Mark-MDO47/RingTheBell/code/lib_commonDFcode/lib_commonDFcode.h

// This ".h" file is actually C-code. Saves me the need to turn it into a true library.

/////////////////////////////////////////////////////////////////////////////////////////////////////////
#if DFPRINTDETAIL
void DFprintDetail(uint8_t type, int value){
  switch (type) {
    case TimeOut:
      Serial.println(F("Time Out!")); break;
    case WrongStack:
      Serial.println(F("Stack Wrong!")); break;
    case DFPlayerCardInserted:
      Serial.println(F("Card Inserted!")); break;
    case DFPlayerCardRemoved:
      Serial.println(F("Card Removed!")); break;
    case DFPlayerCardOnline:
      Serial.println(F("Card Online!")); break;
    case DFPlayerUSBInserted:
      Serial.println("USB Inserted!"); break;
    case DFPlayerUSBRemoved:
      Serial.println("USB Removed!"); break;
    case DFPlayerPlayFinished:
      Serial.print(F("Number:")); Serial.print(value); Serial.println(F(" Play Finished!"));  break;
    case DFPlayerError:
      Serial.print(F("DFPlayerError:"));
      switch (value) {
        case Busy:
          Serial.println(F("Card not found"));
          break;
        case Sleeping:
          Serial.println(F("Sleeping"));
          break;
        case SerialWrongStack:
          Serial.println(F("Get Wrong Stack"));
          break;
        case CheckSumNotMatch:
          Serial.println(F("Check Sum Not Match"));
          break;
        case FileIndexOut:
          Serial.println(F("File Index Out of Bound"));
          break;
        case FileMismatch:
          Serial.println(F("Cannot Find File"));
          break;
        case Advertise:
          Serial.println(F("In Advertise"));
          break;
        default:
          break;
      } // end switch (value)
      break;
    default:
      break;
  }  // end switch (type)
} // end DFprintDetail()
#endif // DFPRINTDETAIL

/////////////////////////////////////////////////////////////////////////////////////////////////////////
// DFstartSound(p_SoundNum, p_Volume) - start p_SoundNum if it is valid
//
// p_SoundNum is the sound file number, range 1 to SOUNDNUM_MAX_VALID
// p_Volume   is the requested vol, range 0 to 30
//
// Had lots of trouble with reliable operation using playMp3Folder. Came to conclusion
//    that it is best to use the most primitive of YX5200 commands.
// Also saw strong correlation of using YX5200 ACK and having even more unreliable
//    operation, so turned that off in DFinit.
// The code checking DPIN_AUDIO_BUSY still needs the delay but 200 millisec is probably overkill.
// There is code checking myDFPlayer.available() that can maybe also be removed now
//    that the dubugging for above is finished. Now that I am using myDFPlayer.play(),
//    it only seems to trigger when I interrupt a playing sound by starting another.
//    It is sort of interesting but not needed.
//
void  DFstartSound(uint16_t p_SoundNum, uint16_t p_Volume) {
  uint16_t idx;
  bool prevHI;
  uint16_t my_SoundNum = p_SoundNum;
  static uint8_t init_minmax = 2;
  static uint32_t prev_msec;
  static uint32_t max_msec = 0;
  static uint32_t min_msec = 999999;
  uint32_t diff_msec = 0;
  uint32_t now_msec = millis();

#if DFPRINTDETAIL
  if (myDFPlayer.available()) {
    Serial.print(F(" DFstartSound ln ")); Serial.print((uint16_t) __LINE__); Serial.println(F(" myDFPlayer problem after volume"));
    DFprintDetail(myDFPlayer.readType(), myDFPlayer.read()); //Print the detail message from DFPlayer to handle different errors and states.
  }
#endif // DFPRINTDETAIL

  myDFPlayer.volume(p_Volume);  // Set volume value. Range from 0 to 30
  myDFPlayer.play(my_SoundNum); //play specific wav in SD: root directory ###.wav; number played is physical copy order; first one copied is 1
  // Serial.print(F("DEBUG DFstartSound myDFPlayer.play(")); Serial.print((uint16_t) my_SoundNum); Serial.println(F(")"));
  gTimerForceSoundActv = millis() + SOUND_ACTIVE_PROTECT; // handle YX5200 problem with interrupting play

  if (init_minmax) {
    init_minmax -= 1;
  }  else {
    diff_msec = now_msec - prev_msec;
    if (diff_msec > max_msec) {
      max_msec = diff_msec;
      // Serial.print(F("max_msec ")); Serial.println(max_msec);
    } else if (diff_msec < min_msec) {
      min_msec = diff_msec;
      // Serial.print(F("min_msec ")); Serial.println(min_msec);
    }
  }
  prev_msec = now_msec;
} // end DFstartSound()

/////////////////////////////////////////////////////////////////////////////////////////////////////////
// DFcheckSoundDone() - returns TRUE if previous sound is complete (DFPlayer/YX5200 is notBusy)
//
// notBusy means (HIGH == digitalRead(DPIN_AUDIO_BUSY)) && (millis() >= gTimerForceSoundActv)
//
//    DPIN_AUDIO_BUSY goes HIGH when sound finished, but may take a while to start being high after sound starts
//    gTimerForceSoundActv is millisec count we have to wait for to before checking DPIN_AUDIO_BUSY
//    so we have to be BOTH (DPIN_AUDIO_BUSY is HIGH) AND (current time is beyond gTimerForceSoundActv)
//
uint8_t DFcheckSoundDone() {
  return (HIGH == digitalRead(DPIN_AUDIO_BUSY)) && (millis() >= gTimerForceSoundActv);
} // end DFcheckSoundDone()

/////////////////////////////////////////////////////////////////////////////////////////////////////////
// DFsetup()
void DFsetup() {
  Serial.println(F("Initializing DFPlayer ... (May take 3~5 seconds)"));
  
  pinMode(DPIN_AUDIO_BUSY,  INPUT_PULLUP); // HIGH when audio stops
  Serial2.begin(9600, SERIAL_8N1, DPIN_HWSRL_RX, DPIN_HWSRL_TX); // this is control to DFPlayer audio player 
  if (!myDFPlayer.begin(Serial2, false, true)) {  // Serial2 to communicate with mp3 player
    Serial.println(F("Unable to begin DFPlayer:"));
    Serial.println(F("1.Please recheck the connection!"));
    Serial.println(F("2.Please insert the SD card!"));
    while(true){
      delay(1);
    }
  }
  myDFPlayer.EQ(DFPLAYER_EQ_BASS); // our speaker is quite small
  myDFPlayer.outputDevice(DFPLAYER_DEVICE_SD); // location of sound files is MicroSD card
  myDFPlayer.volume(SOUND_VOL_MAX);  // Set volume value. From 0 to 30 - FIXME 25 is good
  // delay(3000); // allow bluetooth connection to complete - not using bluetooth; tinny sound from small speaker adds to effect
  delay(1000); // allow DFPlayer to stabilize
  Serial.println(F("DFPlayer Mini online."));

} // end DFsetup()
