Mark-MDO47/RingTheBell/code/RingTheBell/SoundNum.h

// DuelWithBanjos
// Author: https://github.com/Mark-MDO47/
//

#ifndef SOUNDNUM_h

#define SOUNDNUM_h

#define SOUNDNUM_MalletHit    1
#define SOUNDNUM_silence      2
#define SOUNDNUM_RingBell     3
#define SOUNDNUM_MAX_VALID    3 // Last valid sound number
#define SOUNDNUM_save_for_OTA 4
#define SOUNDNUM_MAX_PLUS     4 // includes the saved index for OTA

#endif // SOUNDNUM_h
